innoveworkshop/Bipolary/Simulations/Shunt Regulator.asc

C1: cap; 1µ
C2: cap; 1000µ
C3: cap; {C}
C4: cap; 1µ
C5: cap; {C}
D1: LED; LedRed
Q1: npn; BC847C
Q2: pnp; TIP32C
Q3: pnp; BC857C
Q4: pnp; BC857C
Q5: pnp; TIP32C
Q6: pnp; BC857C
Q7: npn; TIP31C
R1: res; 220
R2: res; 88k
R3: res; 20k
R6: res; 6
R7: res; 10
R8: res; 1Meg
R10: res; 10k
R11: res; 4.7k
R13: res; 1Meg
V1: voltage; SINE(15V 1V 100Hz)
V2: voltage; SINE(1V 0.5V 20Hz)
Named nets: 0, V+, Output, ACOutput, ACV+
.tran 0 20000ms 0 100u startup
SINE(15V 1V 100Hz)
This is just simulating a
load on the circuit.
SINE(1V 0.5V 20Hz)
.step param C 0 100u 10u
.param C 20u
