innoveworkshop/Bipolary/Simulations/Common-Emitter Series Feedback.asc

C1: cap; 100µ
C2: cap; 1000µ
C3: cap; 1000µ
Q1: npn; BC817
R1: res; 10k
R2: res; 65k
R3: res; 100k
R4: res; 1k
R5: res; 5k
R6: res; 500
Rload: res; 1Meg
V1: voltage; 12V
V2: voltage; SINE(0 100mV {freq}); AC 100mV
Named nets: V+, 0, Input, Output
.tran 0 10ms 0 1u
.options plotwinsize=0
.four {freq} 10 v(output)
.param freq=1k
