innoveworkshop/Bipolary/Simulations/Common-Emitter Shunt Feedback.asc

C1: cap; 100µ
C2: cap; 1000µ
Q1: npn; BC817
R1: res; 11k
R2: res; 100k
R3: res; 100k
R4: res; 22k
R5: res; 10k
Rload1: res; 1Meg
V1: voltage; 12V
V2: voltage; SINE(0 100mV {freq}); AC 100mV
Named nets: V+, 0, Input, Output
.tran 0 10ms 0 1u
.options plotwinsize=0
.four {freq} 10 v(output)
.param freq=1k
