innoveworkshop/Bipolary/Simulations/Headphone Amplifier (Rev A).asc

C1: cap; 1000µ
C2: cap; 4µ7
C3: cap; 10p
C4: cap; 0.01µ
Q1: npn; BC847
Q2: pnp; BC857C
Q3: npn; BC847
Q4: pnp; BC857C
Q5: pnp; BD136P
Q6: npn; BD135P
Q7: npn; BC847
R1: res; 470
R2: res; 330
R3: res; 10k
R4: res; 7k5
R5: res; 10k
R6: res; 1k
R7: res; 10k
R8: res; 68k
R9: res; 100k
R10: res; 4k7
R11: res; 10
R12: res; 10
Rload: res; 300
V2: voltage; 12V
V3: voltage; SINE(0 500mV {freq}); AC 500mV
Named nets: 0, V+, Output, Input, DCOutput
.tran 0 50ms 0 1u
.options plotwinsize=0
.four {freq} 10 v(output)
.param freq=20k
Use a potentiometer in place
of R4 to adjust the output midpoint.
.ac dec 10 1 100k
